dwblair/pico-co2/REV_X/hardware/references/scd30_power_setup.png

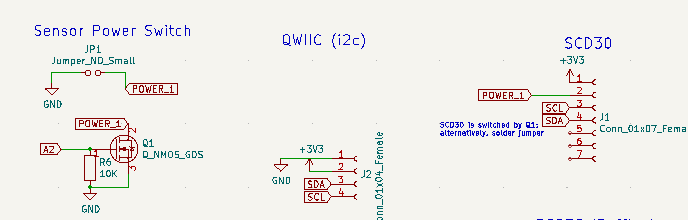
REV_X/hardware/references/scd30_power_setup.png
