dwblair/pico-co2/REV_X/firmware/cpy_8/testdisplay.py

import board
import busio
import displayio
import terminalio
from adafruit_display_text import label
import adafruit_displayio_ssd1306
import time

displayio.release_displays()

i2c = busio.I2C(scl=board.GP1, sda=board.GP0)

# i2c = board.STEMMA_I2C()  # For using the built-in STEMMA QT connector on a microcontroller
display_bus = displayio.I2CDisplay(i2c, device_address=0x3C)
time.sleep(1)
display = adafruit_displayio_ssd1306.SSD1306(display_bus, width=128, height=32)

# Make the display context
splash = displayio.Group()
display.show(splash)

color_bitmap = displayio.Bitmap(128, 32, 1)
color_palette = displayio.Palette(1)
color_palette[0] = 0xFFFFFF  # White

bg_sprite = displayio.TileGrid(color_bitmap, pixel_shader=color_palette, x=0, y=0)
splash.append(bg_sprite)

# Draw a smaller inner rectangle
inner_bitmap = displayio.Bitmap(118, 24, 1)
inner_palette = displayio.Palette(1)
inner_palette[0] = 0x000000  # Black
inner_sprite = displayio.TileGrid(inner_bitmap, pixel_shader=inner_palette, x=5, y=4)
splash.append(inner_sprite)

# Draw a label
text = "Hello World!"
text_area = label.Label(terminalio.FONT, text=text, color=0xFFFF00, x=28, y=15)
splash.append(text_area)

time.sleep(10)

while True:
    pass
