dwblair/pico-co2/REV_X/firmware/cpy_8/ntp.py

# SPDX-FileCopyrightText: 2022 Liz Clark for Adafruit Industries
#
# SPDX-License-Identifier: MIT

import os
import adafruit_ntp
import socketpool
import time
import wifi


#  connect to SSID
wifi.radio.connect(os.getenv('WIFI_SSID'), os.getenv('WIFI_PASSWORD'))

pool = socketpool.SocketPool(wifi.radio)

pool = socketpool.SocketPool(wifi.radio)
ntp = adafruit_ntp.NTP(pool, tz_offset=0)

while True:
    print(ntp.datetime)
    time.sleep(1)
