dwblair/pico-co2/REV_X/firmware/cpy_8/wifiscan.py

# SPDX-FileCopyrightText: 2022 Liz Clark for Adafruit Industries
#
# SPDX-License-Identifier: MIT

import os
import ipaddress
import wifi
import socketpool

print()
print("Connecting to WiFi")

for network in wifi.radio.start_scanning_networks():
    print("\t%s\t\tRSSI: %d\tChannel: %d" % (str(network.ssid, "utf-8"),
            network.rssi, network.channel))
wifi.radio.stop_scanning_networks()
